rajeev-t/object-sorting-robot/cad/sensors-and-mounts/rgb-sensor-mount.SLDPRT

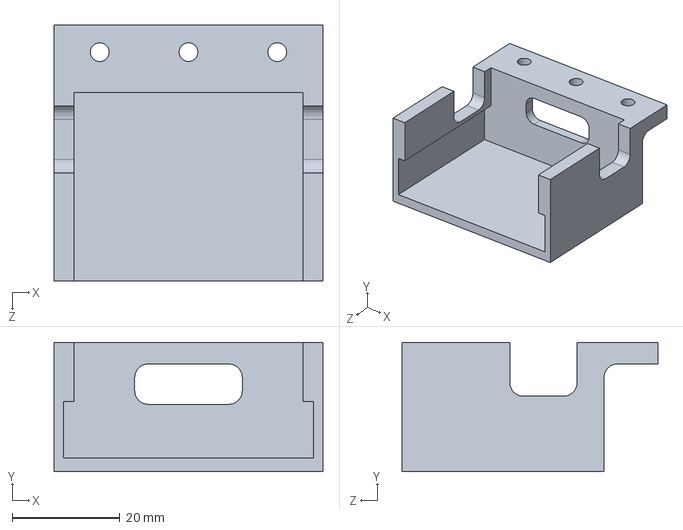
[picture p30: CAD file, 2023-06-07]
cad/sensors-and-mounts/rgb-sensor-mount.SLDPRT
50.0 x 24.0 x 47.5 mm
