rajeev-t/object-sorting-robot/cad/STLs/mount-L.STL

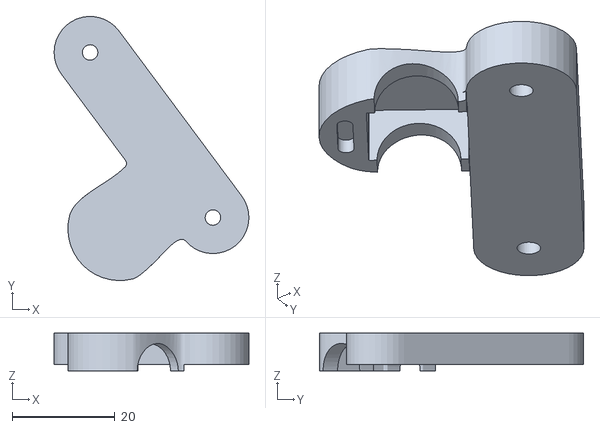
[picture p31: CAD file, 2023-06-07]
cad/STLs/mount-L.STL
37.9 x 51.3 x 7.35
