rajeev-t/object-sorting-robot/cad/suction-components/suction-mount-L.SLDPRT

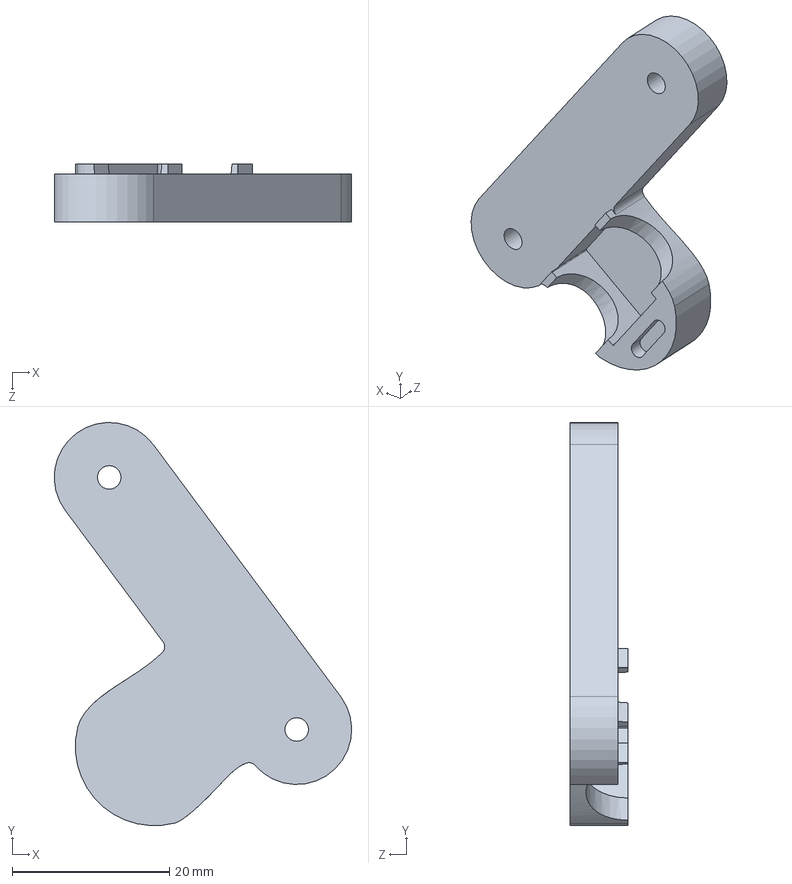
[picture p32: CAD file, 2023-06-07]
cad/suction-components/suction-mount-L.SLDPRT
37.9 x 51.3 x 7.35 mm
