rajeev-t/object-sorting-robot/cad/dummy-components/dummy-pump.SLDPRT

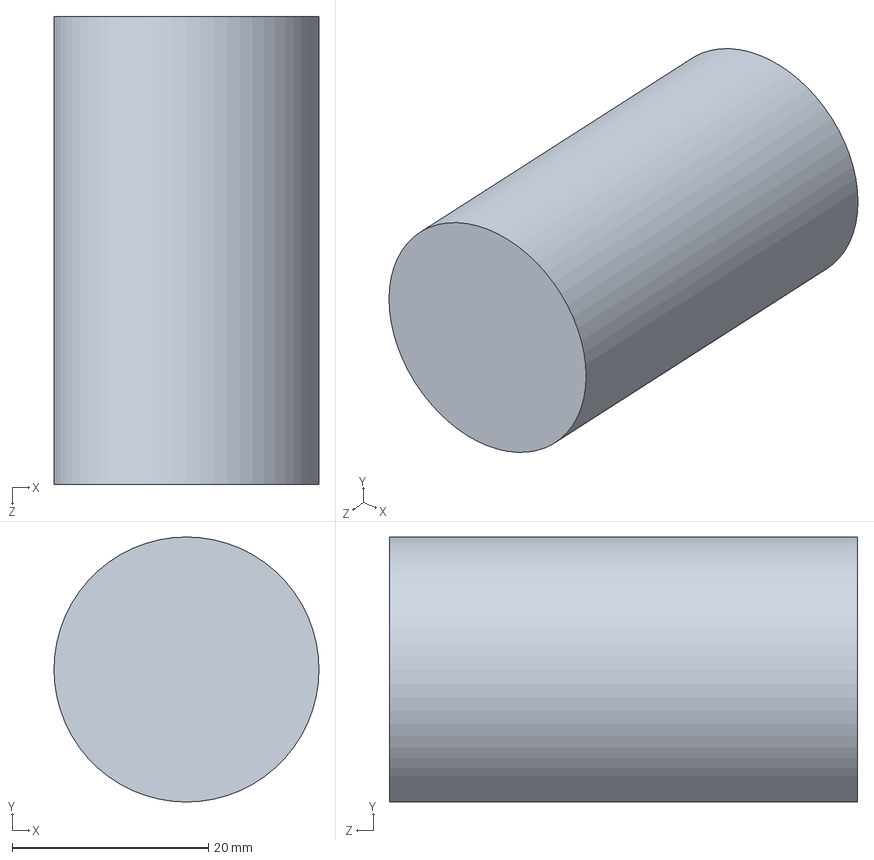
[picture p33: CAD file, 2023-06-07]
cad/dummy-components/dummy-pump.SLDPRT
27.0 x 27.0 x 47.7 mm
