rajeev-t/object-sorting-robot/cad/housing-components/housing-lid.SLDPRT

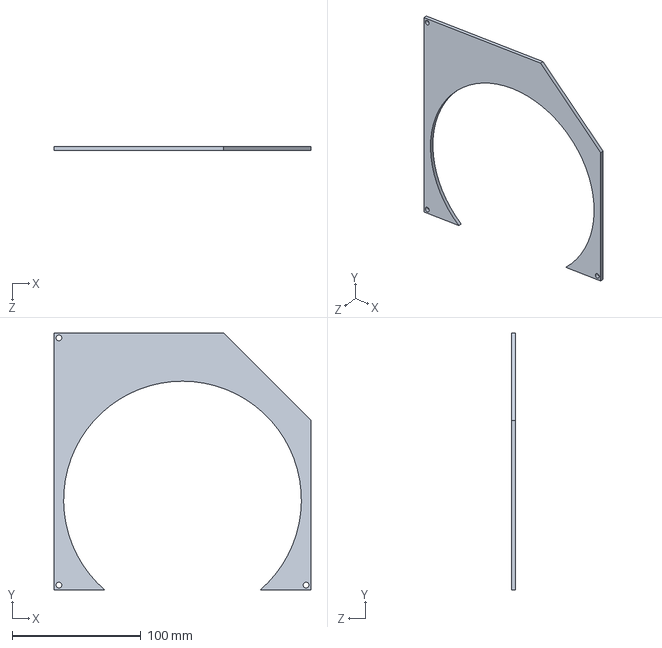
[picture p34: CAD file, 2023-06-07]
cad/housing-components/housing-lid.SLDPRT
200.0 x 200.0 x 3.50 mm
