rajeev-t/object-sorting-robot/cad/links/link-2.SLDPRT

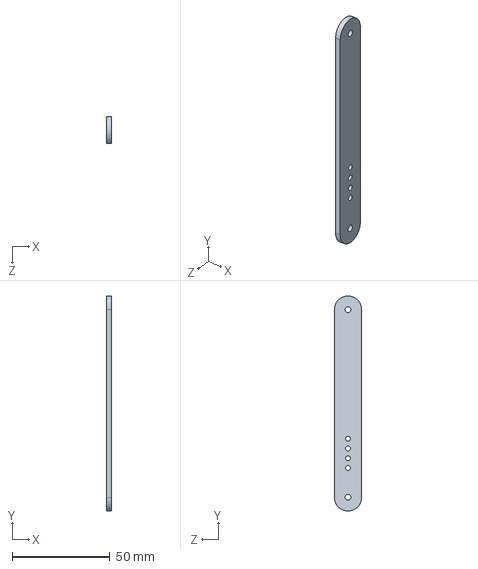
[picture p35: CAD file, 2023-06-07]
cad/links/link-2.SLDPRT
2.50 x 110.0 x 14.0 mm
