rajeev-t/object-sorting-robot/cad/dummy-components/dummy-pico.SLDPRT

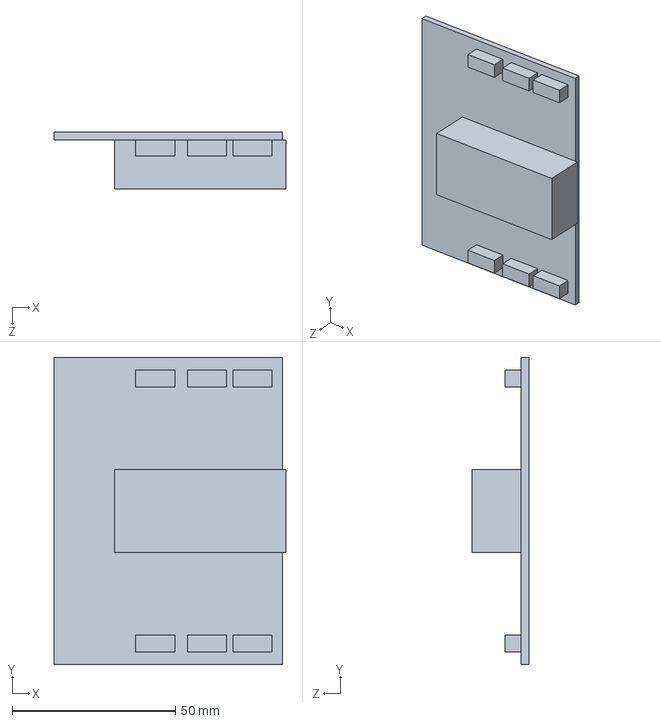
[picture p36: CAD file, 2023-06-07]
cad/dummy-components/dummy-pico.SLDPRT
71.0 x 94.0 x 17.3 mm
