rajeev-t/object-sorting-robot/cad/links/link-3.SLDPRT

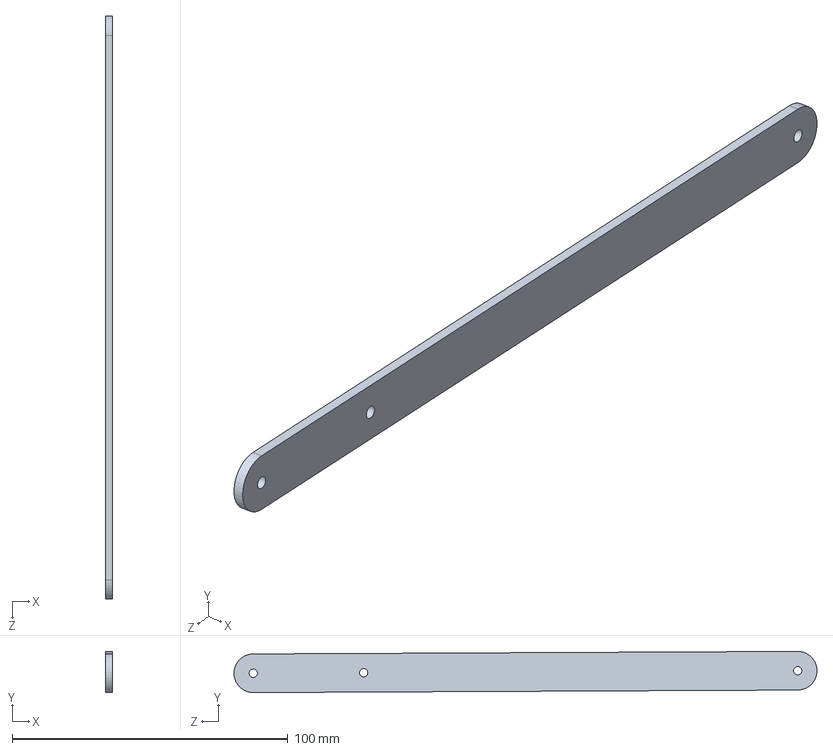
[picture p37: CAD file, 2023-06-07]
cad/links/link-3.SLDPRT
2.50 x 14.9 x 211.2 mm
