rajeev-t/object-sorting-robot/cad/dummy-components/dummy-breadboard.SLDPRT

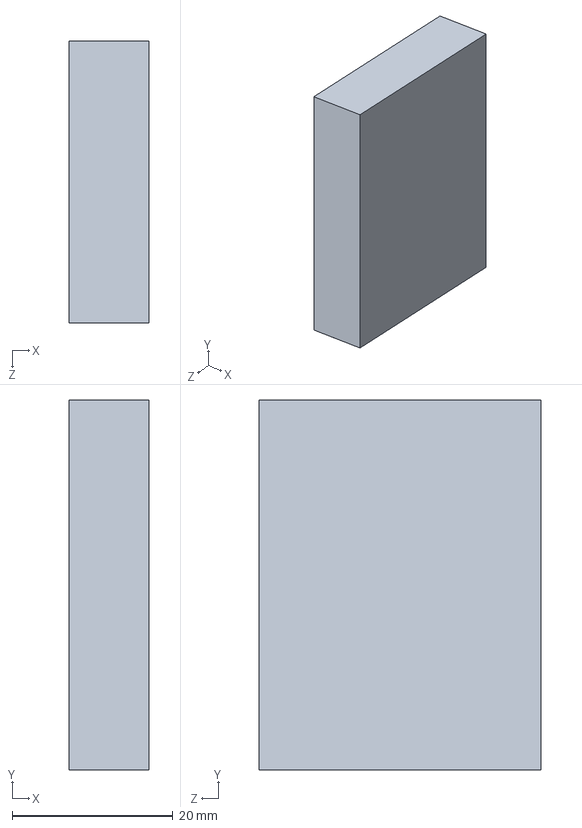
[picture p38: CAD file, 2023-06-07]
cad/dummy-components/dummy-breadboard.SLDPRT
10.0 x 46.0 x 35.0 mm
