rajeev-t/object-sorting-robot/cad/links/base.SLDPRT

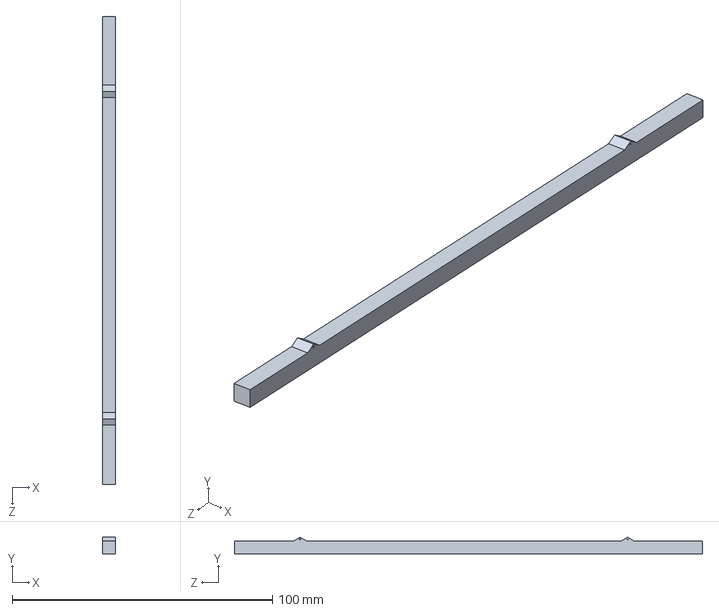
[picture p39: CAD file, 2023-06-07]
cad/links/base.SLDPRT
5.00 x 6.40 x 180.0 mm
