rajeev-t/object-sorting-robot/cad/STLs/sorted-2.STL

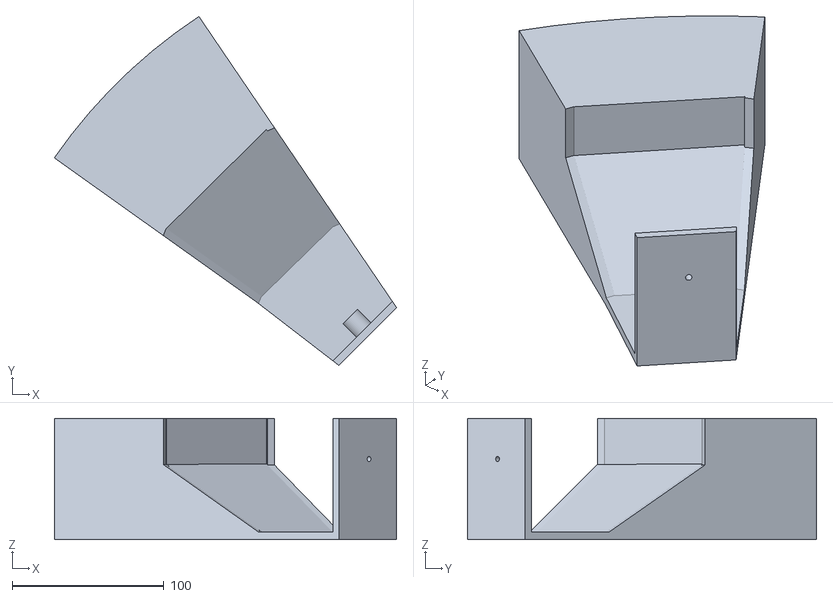
[picture p40: CAD file, 2023-06-07]
cad/STLs/sorted-2.STL
226.0 x 230.3 x 80.0
