rajeev-t/object-sorting-robot/cad/suction-components/suction-mount-R.SLDPRT

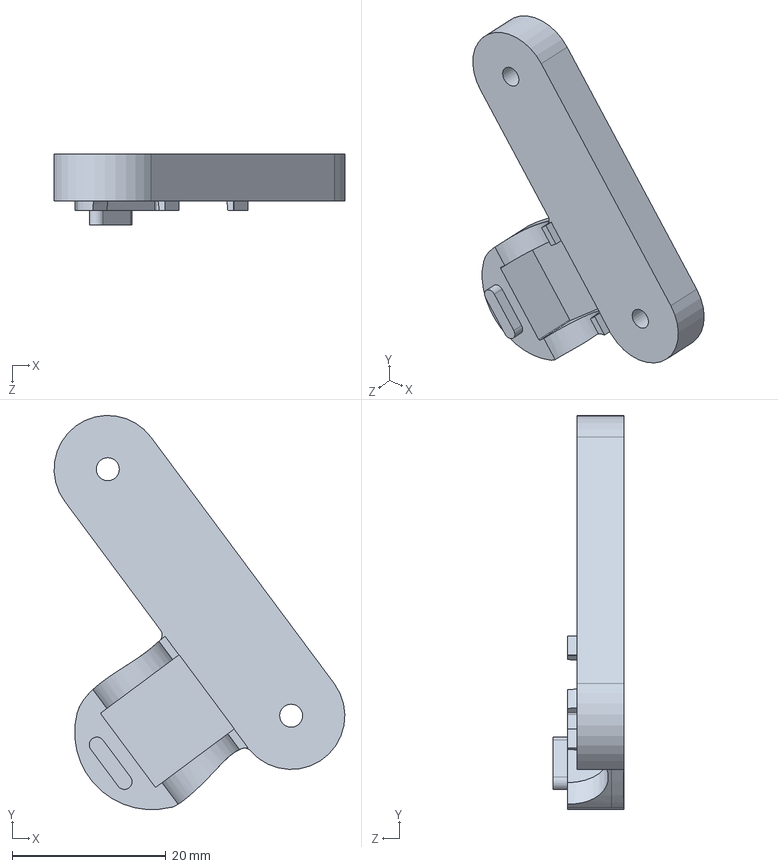
[picture p41: CAD file, 2023-06-07]
cad/suction-components/suction-mount-R.SLDPRT
37.9 x 51.3 x 9.19 mm
