rajeev-t/object-sorting-robot/cad/links/link-4.SLDPRT

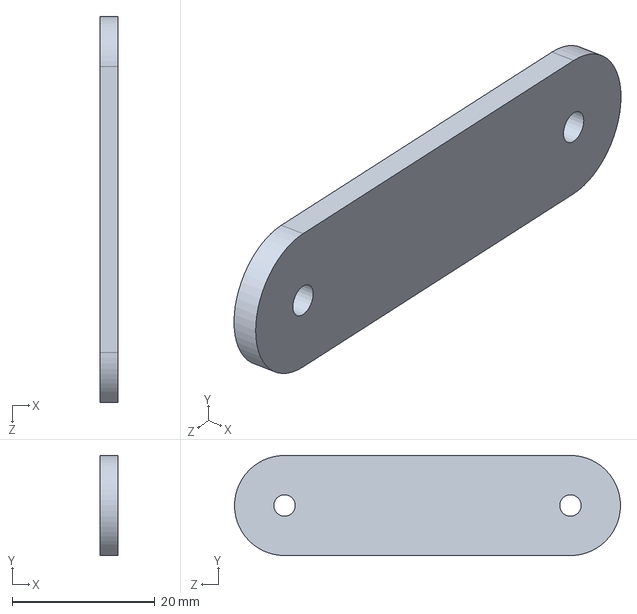
[picture p42: CAD file, 2023-06-07]
cad/links/link-4.SLDPRT
2.50 x 14.0 x 54.0 mm
