rajeev-t/object-sorting-robot/cad/suction-components/suction-cup.SLDPRT

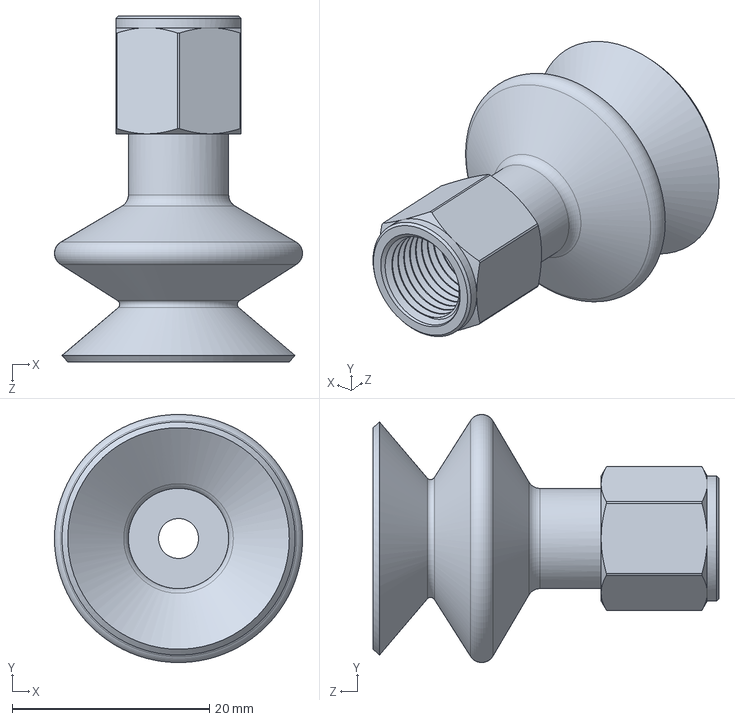
[picture p43: CAD file, 2023-06-07]
cad/suction-components/suction-cup.SLDPRT
25.1 x 25.1 x 35.1 mm
