rajeev-t/object-sorting-robot/cad/links/link-2b.SLDPRT

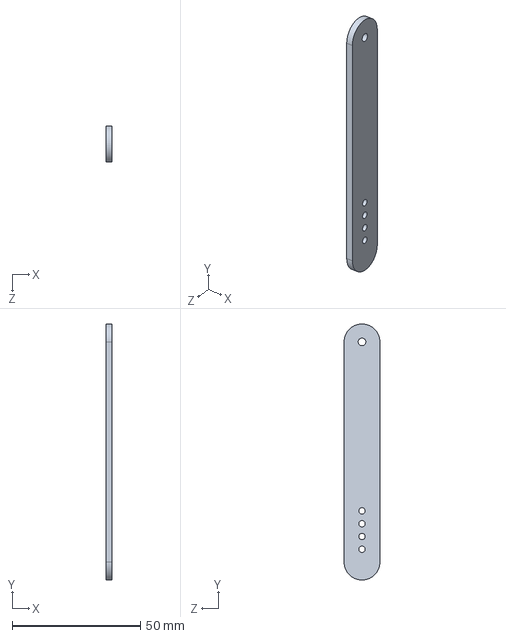
[picture p44: CAD file, 2023-06-07]
cad/links/link-2b.SLDPRT
2.50 x 100.0 x 14.0 mm
