rajeev-t/object-sorting-robot/cad/STLs/sorted-1.STL

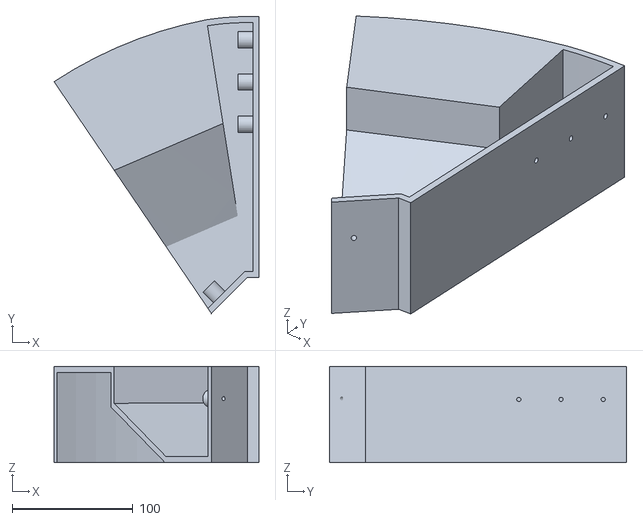
[picture p45: CAD file, 2023-06-07]
cad/STLs/sorted-1.STL
169.9 x 246.3 x 80.0
