rajeev-t/object-sorting-robot/cad/suction-components/suction-adapter.SLDPRT

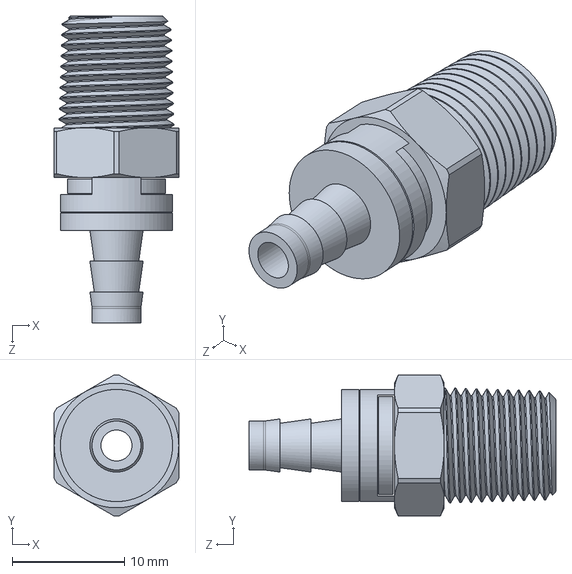
[picture p46: CAD file, 2023-06-07]
cad/suction-components/suction-adapter.SLDPRT
11.1 x 12.6 x 27.4 mm
