rajeev-t/object-sorting-robot/cad/links/link-1b.SLDPRT

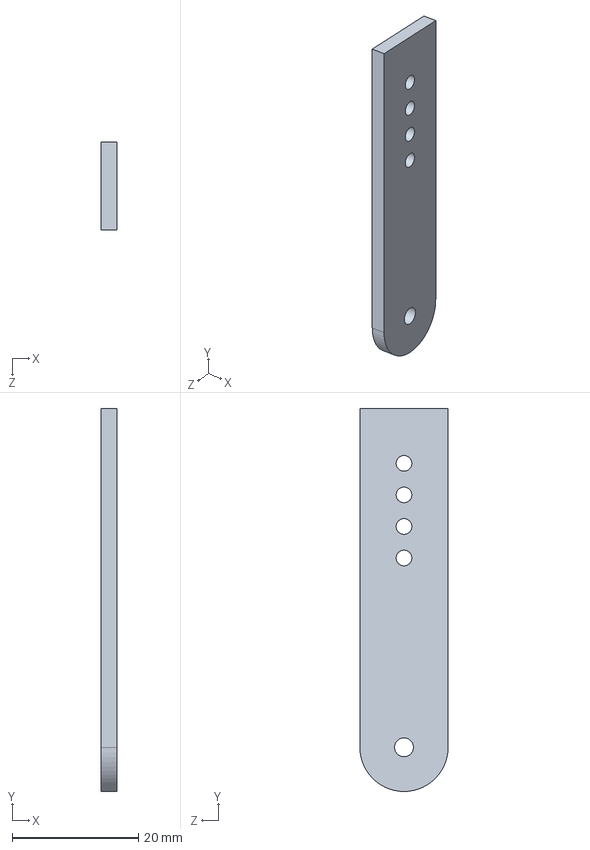
[picture p47: CAD file, 2023-06-07]
cad/links/link-1b.SLDPRT
2.50 x 60.7 x 14.0 mm
