rajeev-t/object-sorting-robot/cad/STLs/sorted-3.STL

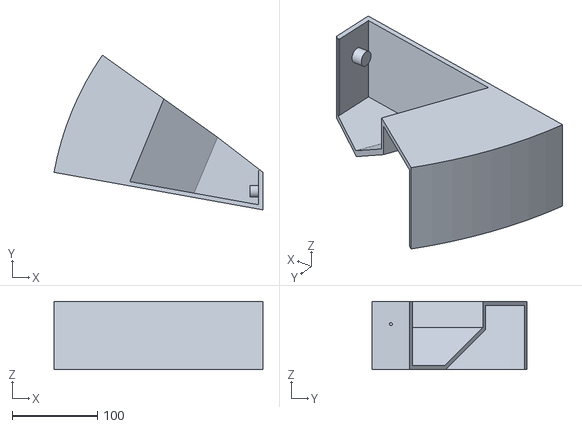
[picture p48: CAD file, 2023-06-07]
cad/STLs/sorted-3.STL
244.5 x 181.1 x 80.0
