rajeev-t/object-sorting-robot/test-or-calibration/servo_base.py

# Dependencies
from machine import Pin, PWM
import time

servo = PWM(Pin(15))
servo.freq(100)

duty_unsorted = int((6/80)*65535)
duty_90_from_unsorted = int((14/80)*65535)
duty_test = int((12/80)*65535)

#servo.duty_u16(duty_unsorted)
servo.duty_u16(duty_90_from_unsorted)

#while True:
 #   servo.duty_u16(duty_unsorted)
  #  time.sleep(2)
   # servo.duty_u16(duty_90_from_unsorted)
    #time.sleep(2)
