rajeev-t/object-sorting-robot/media/photos/initial-wiring.jpeg

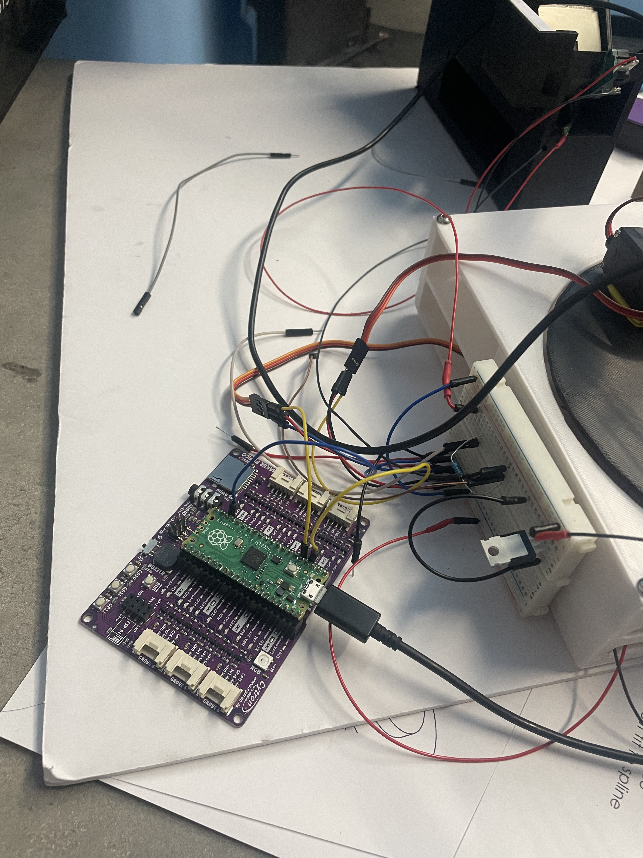
media/photos/initial-wiring.jpeg
